leonardoward/eja-m-pcb-design/Images/Before Routing.png

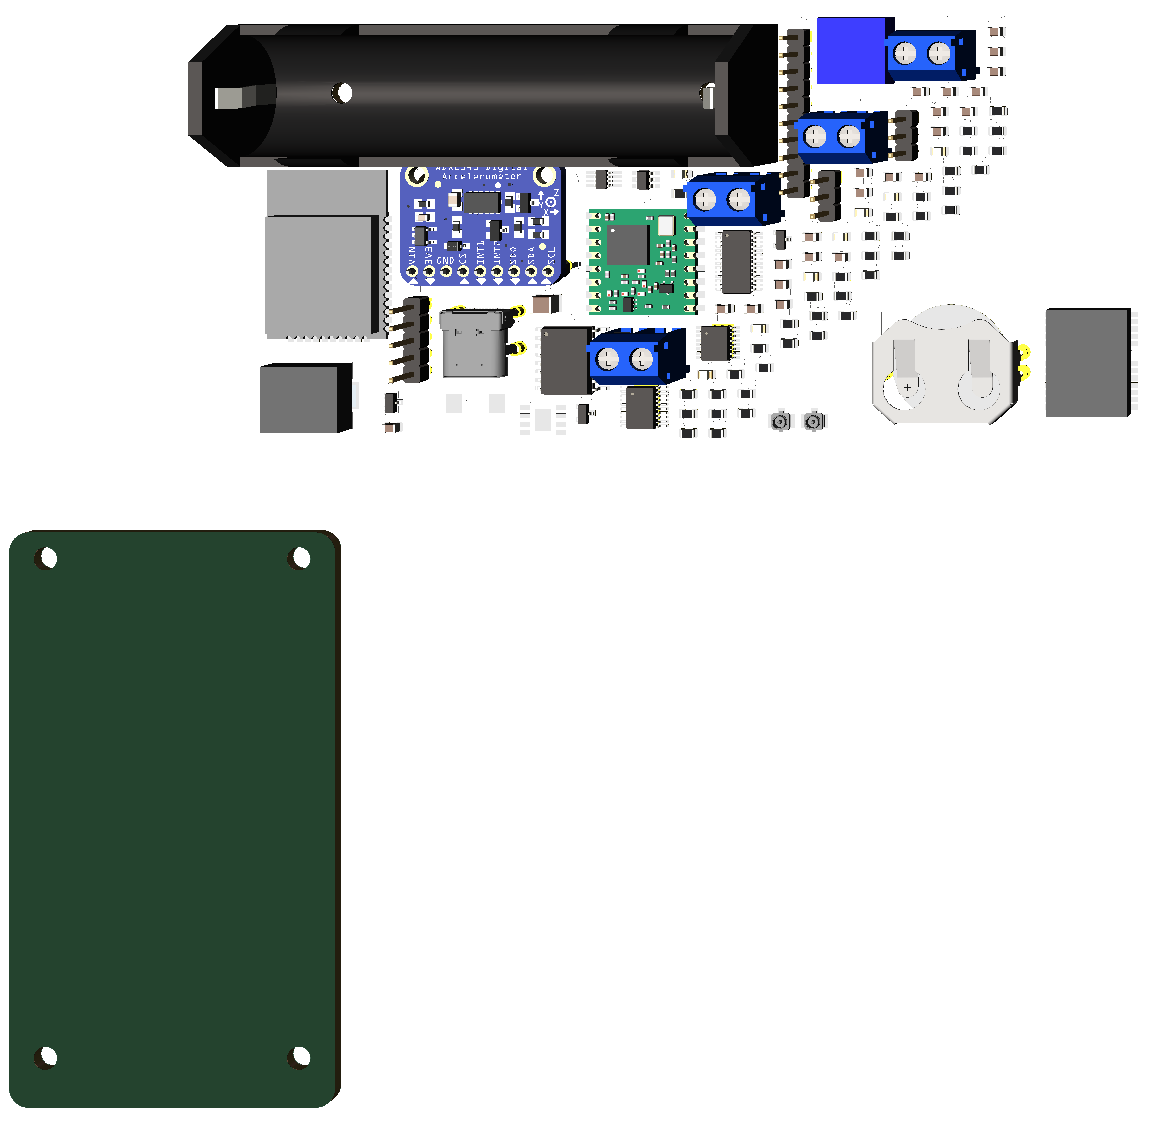
Images/Before Routing.png
